Gabouin/perdican-V1/images/FrontPCBPERDICAN.png

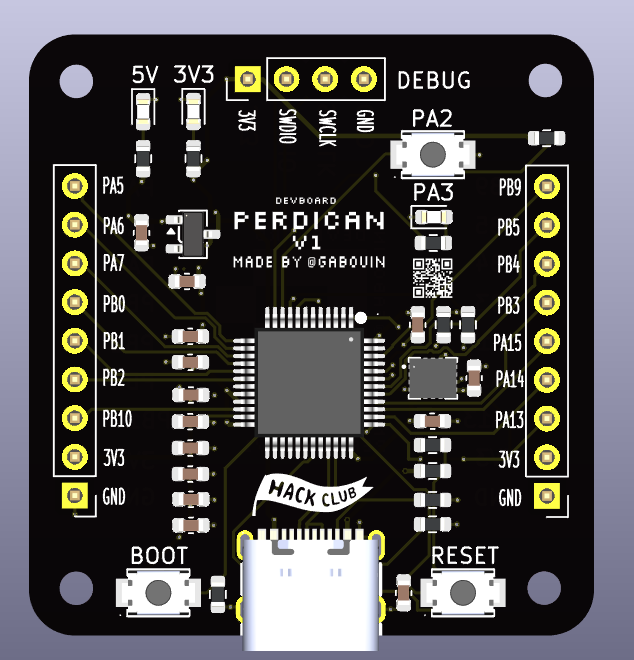
images/FrontPCBPERDICAN.png
