Gabouin/perdican-V1/images/PCBallPERDICAN.png

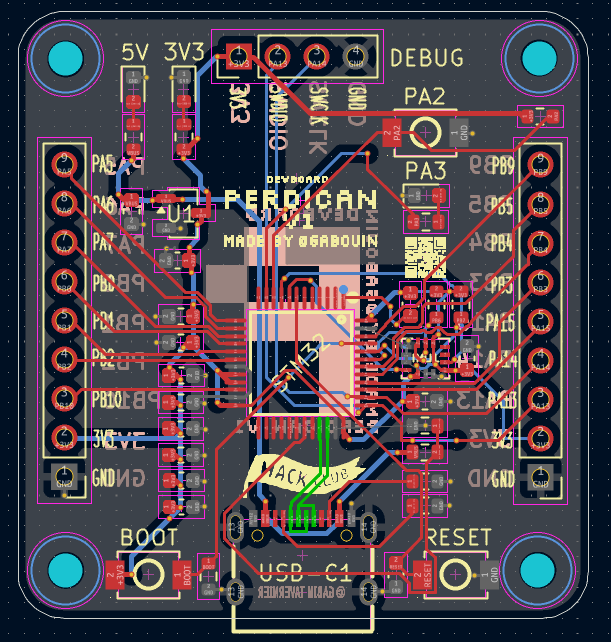
images/PCBallPERDICAN.png
